dvhx/pedal-snow-white-autowah/kicad/pcb-1.png

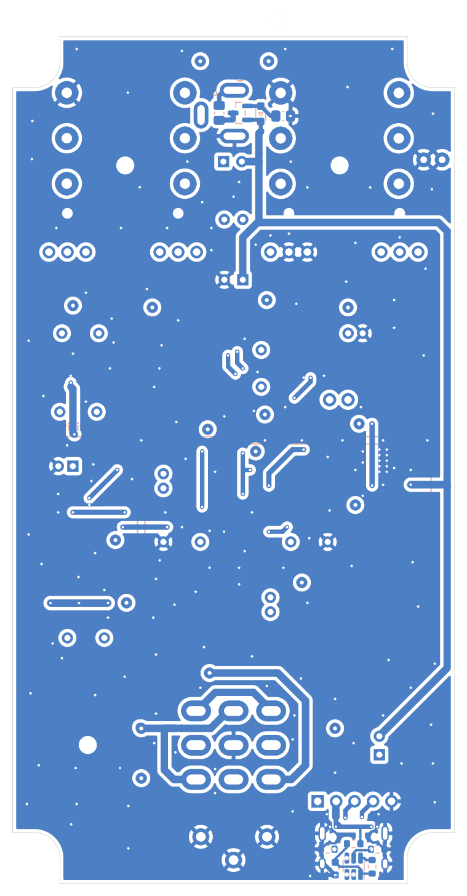
kicad/pcb-1.png
