dvhx/pedal-snow-white-autowah/kicad/pcb-2.png

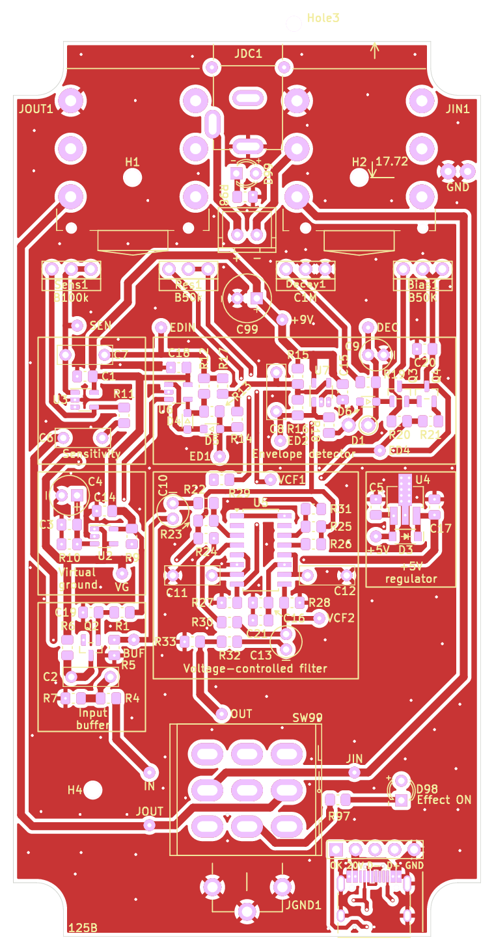
kicad/pcb-2.png
