dvhx/pedal-snow-white-autowah/photo/pcb/thumb/rotated1.jpg

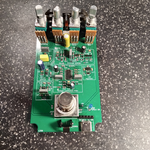
photo/pcb/thumb/rotated1.jpg
