dvhx/pedal-snow-white-autowah/photo/pcb/thumb/rotated3.jpg

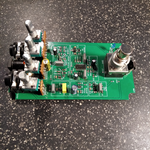
photo/pcb/thumb/rotated3.jpg
