dvhx/pedal-snow-white-autowah/photo/pcb/thumb/rotated4.jpg

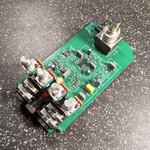
photo/pcb/thumb/rotated4.jpg
