dvhx/pedal-snow-white-autowah/photo/pcb/thumb/rotated5.jpg

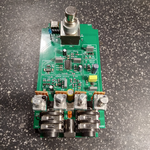
photo/pcb/thumb/rotated5.jpg
