dvhx/pedal-snow-white-autowah/photo/pcb/thumb/rotated6.jpg

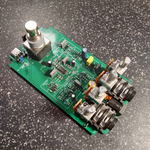
photo/pcb/thumb/rotated6.jpg
