dvhx/pedal-snow-white-autowah/photo/pcb/thumb/rotated7.jpg

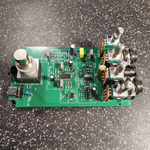
photo/pcb/thumb/rotated7.jpg
